kinggh0stee/WellD/hardware/pcb/interfaces.kicad_sch

## KiCad design hardware/pcb/interfaces.kicad_sch (2026-07-22, an earlier design)

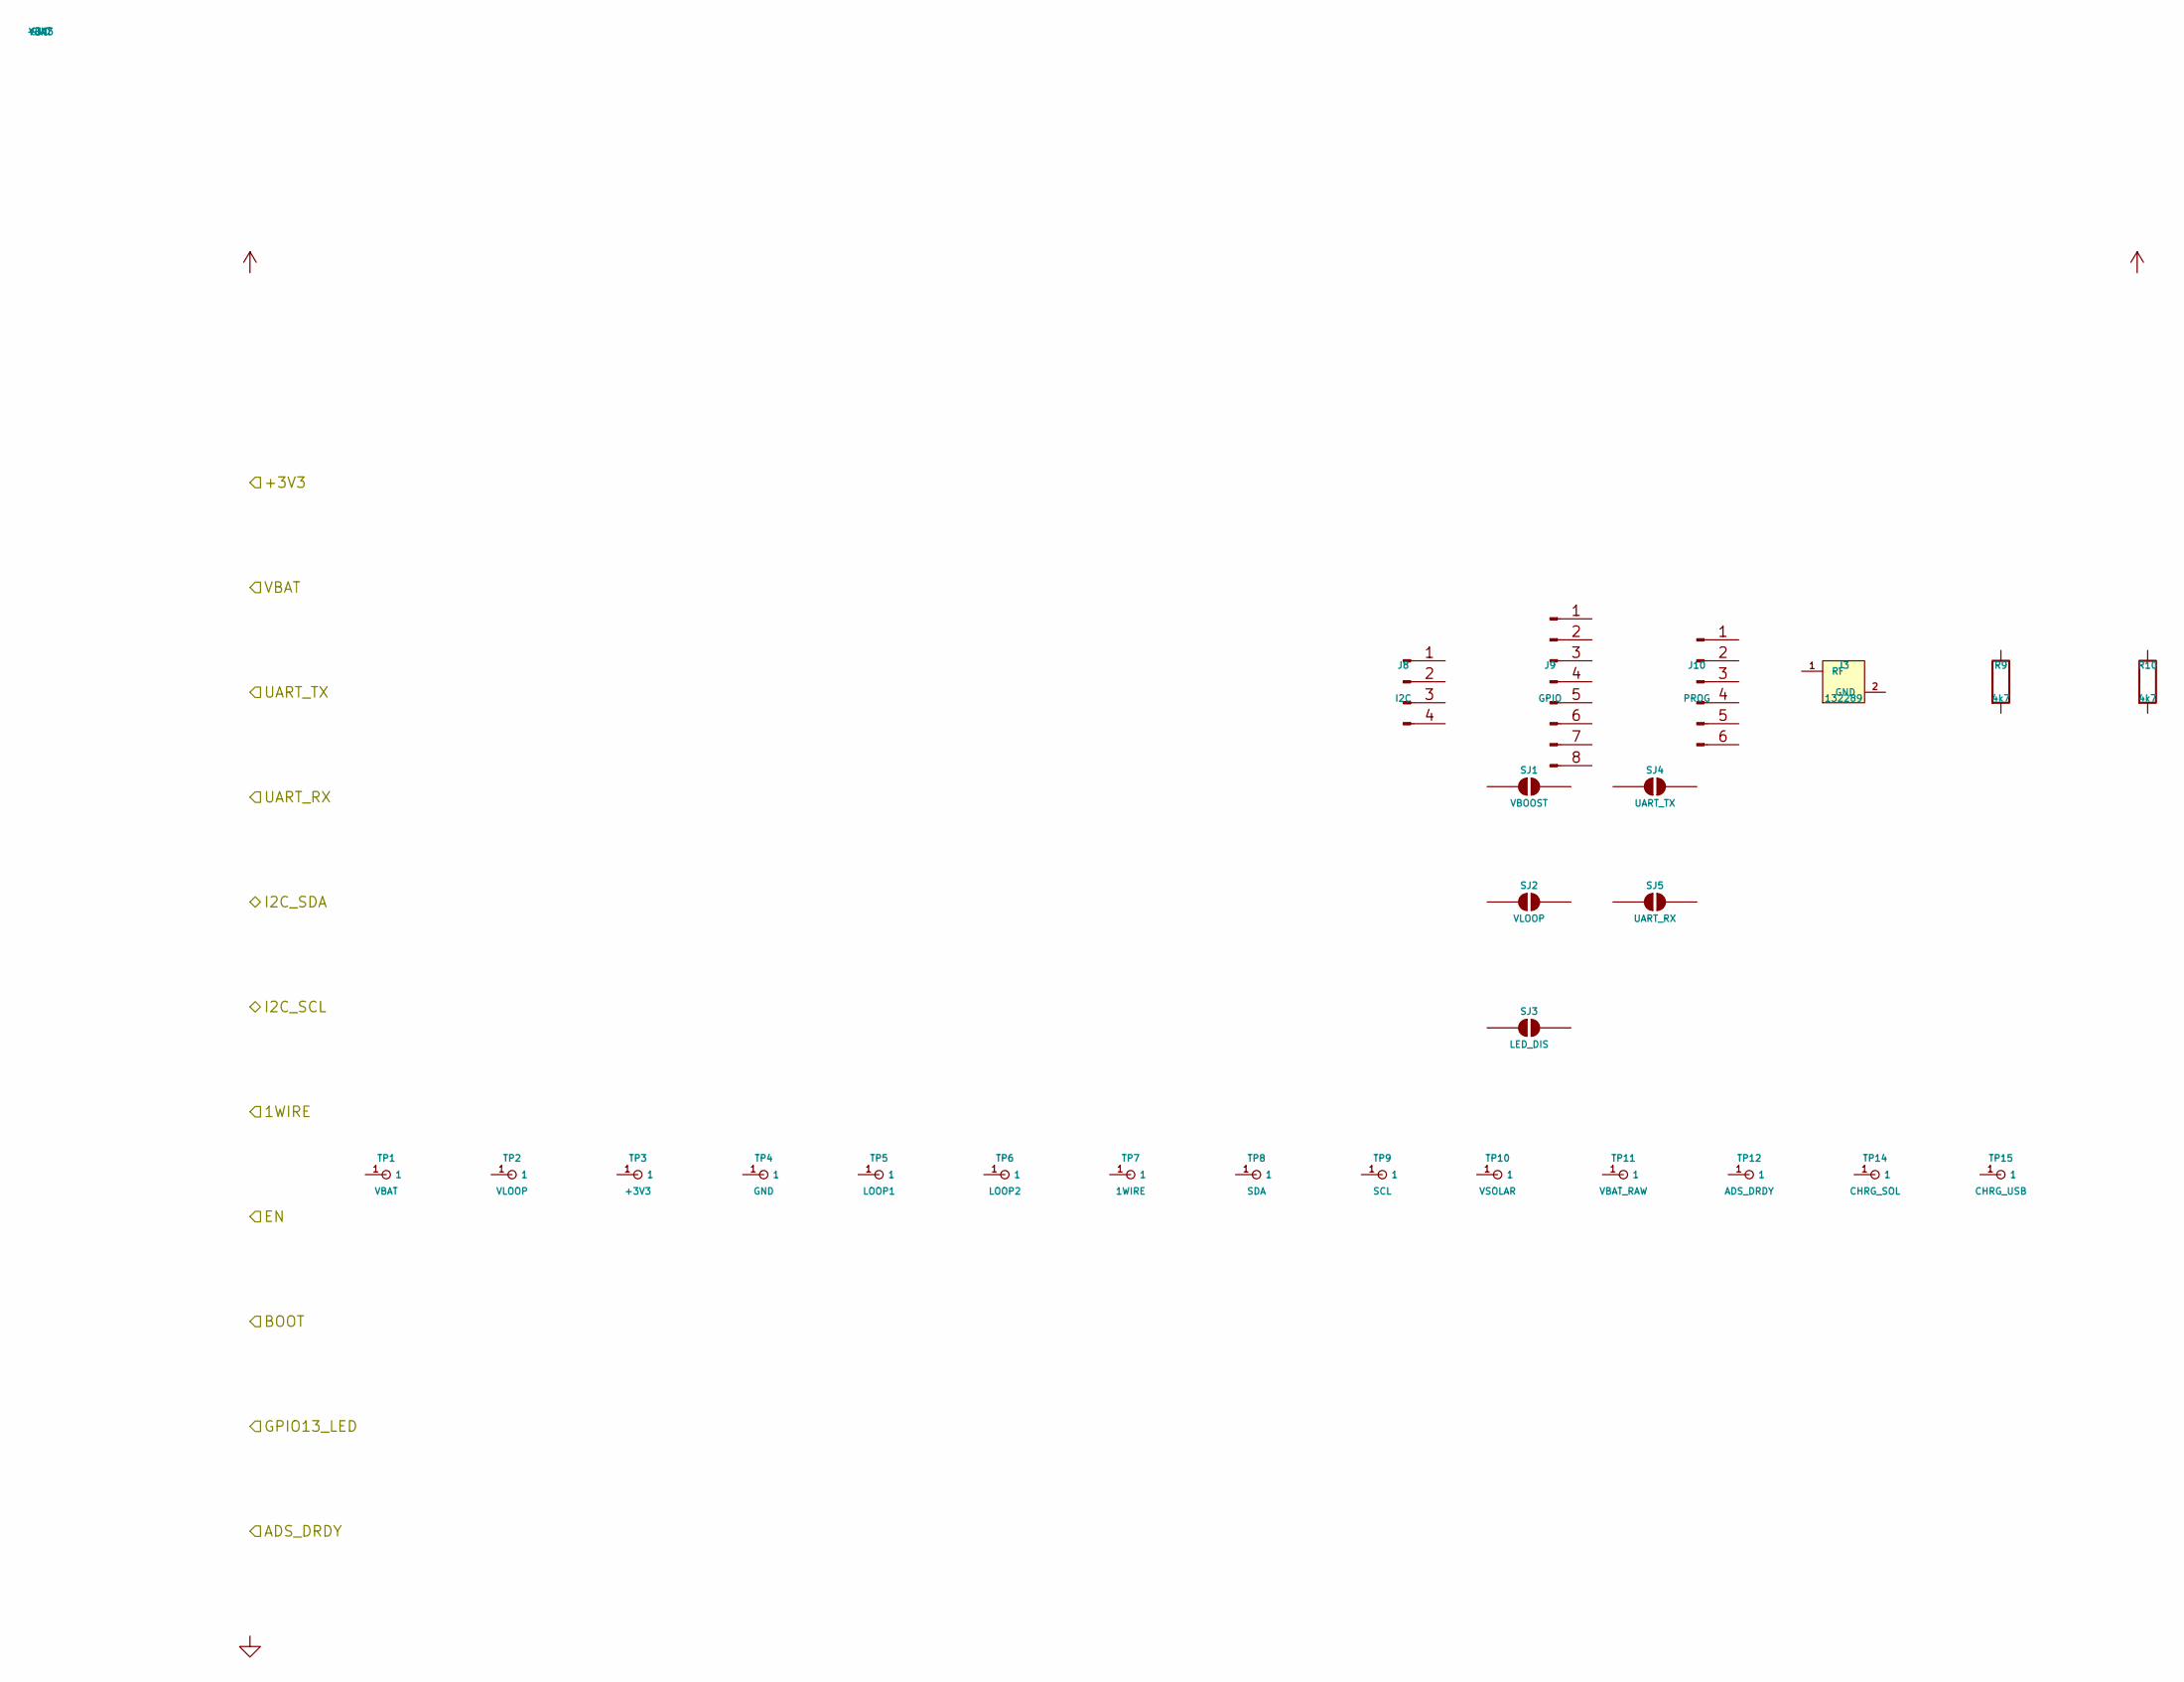
[picture p2: schematic interfaces.kicad_sch]

Parts:
J3: 132289; SMA_Amphenol_132289_EdgeMount
J8: I2C; PinHeader_1x04_P2.54mm_Vertical
J9: GPIO; PinHeader_1x08_P2.54mm_Vertical
J10: PROG; PinHeader_1x06_P1.27mm_Vertical
R9, R10: 4k7; R_0402_1005Metric
SJ1: VBOOST; SolderJumper-2_P1.3mm_Open_Pad1.0x1.5mm
SJ2: VLOOP; SolderJumper-2_P1.3mm_Open_Pad1.0x1.5mm
SJ3: LED_DIS; SolderJumper-2_P1.3mm_Open_Pad1.0x1.5mm
SJ4: UART_TX; SolderJumper-2_P1.3mm_Open_Pad1.0x1.5mm
SJ5: UART_RX; SolderJumper-2_P1.3mm_Open_Pad1.0x1.5mm
TP1: VBAT; TestPoint_Pad_1.0x1.0mm
TP2: VLOOP; TestPoint_Pad_1.0x1.0mm
TP3: +3V3; TestPoint_Pad_1.0x1.0mm
TP4: GND; TestPoint_Pad_1.0x1.0mm
TP5: LOOP1; TestPoint_Pad_1.0x1.0mm
TP6: LOOP2; TestPoint_Pad_1.0x1.0mm
TP7: 1WIRE; TestPoint_Pad_1.0x1.0mm
TP8: SDA; TestPoint_Pad_1.0x1.0mm
TP9: SCL; TestPoint_Pad_1.0x1.0mm
TP10: VSOLAR; TestPoint_Pad_1.0x1.0mm
TP11: VBAT_RAW; TestPoint_Pad_1.0x1.0mm
TP12: ADS_DRDY; TestPoint_Pad_1.0x1.0mm
TP14: CHRG_SOL; TestPoint_Pad_1.0x1.0mm
TP15: CHRG_USB; TestPoint_Pad_1.0x1.0mm
