kinggh0stee/WellD/hardware/pcb/power.kicad_sch

## KiCad design hardware/pcb/power.kicad_sch (2026-07-22, an earlier design)

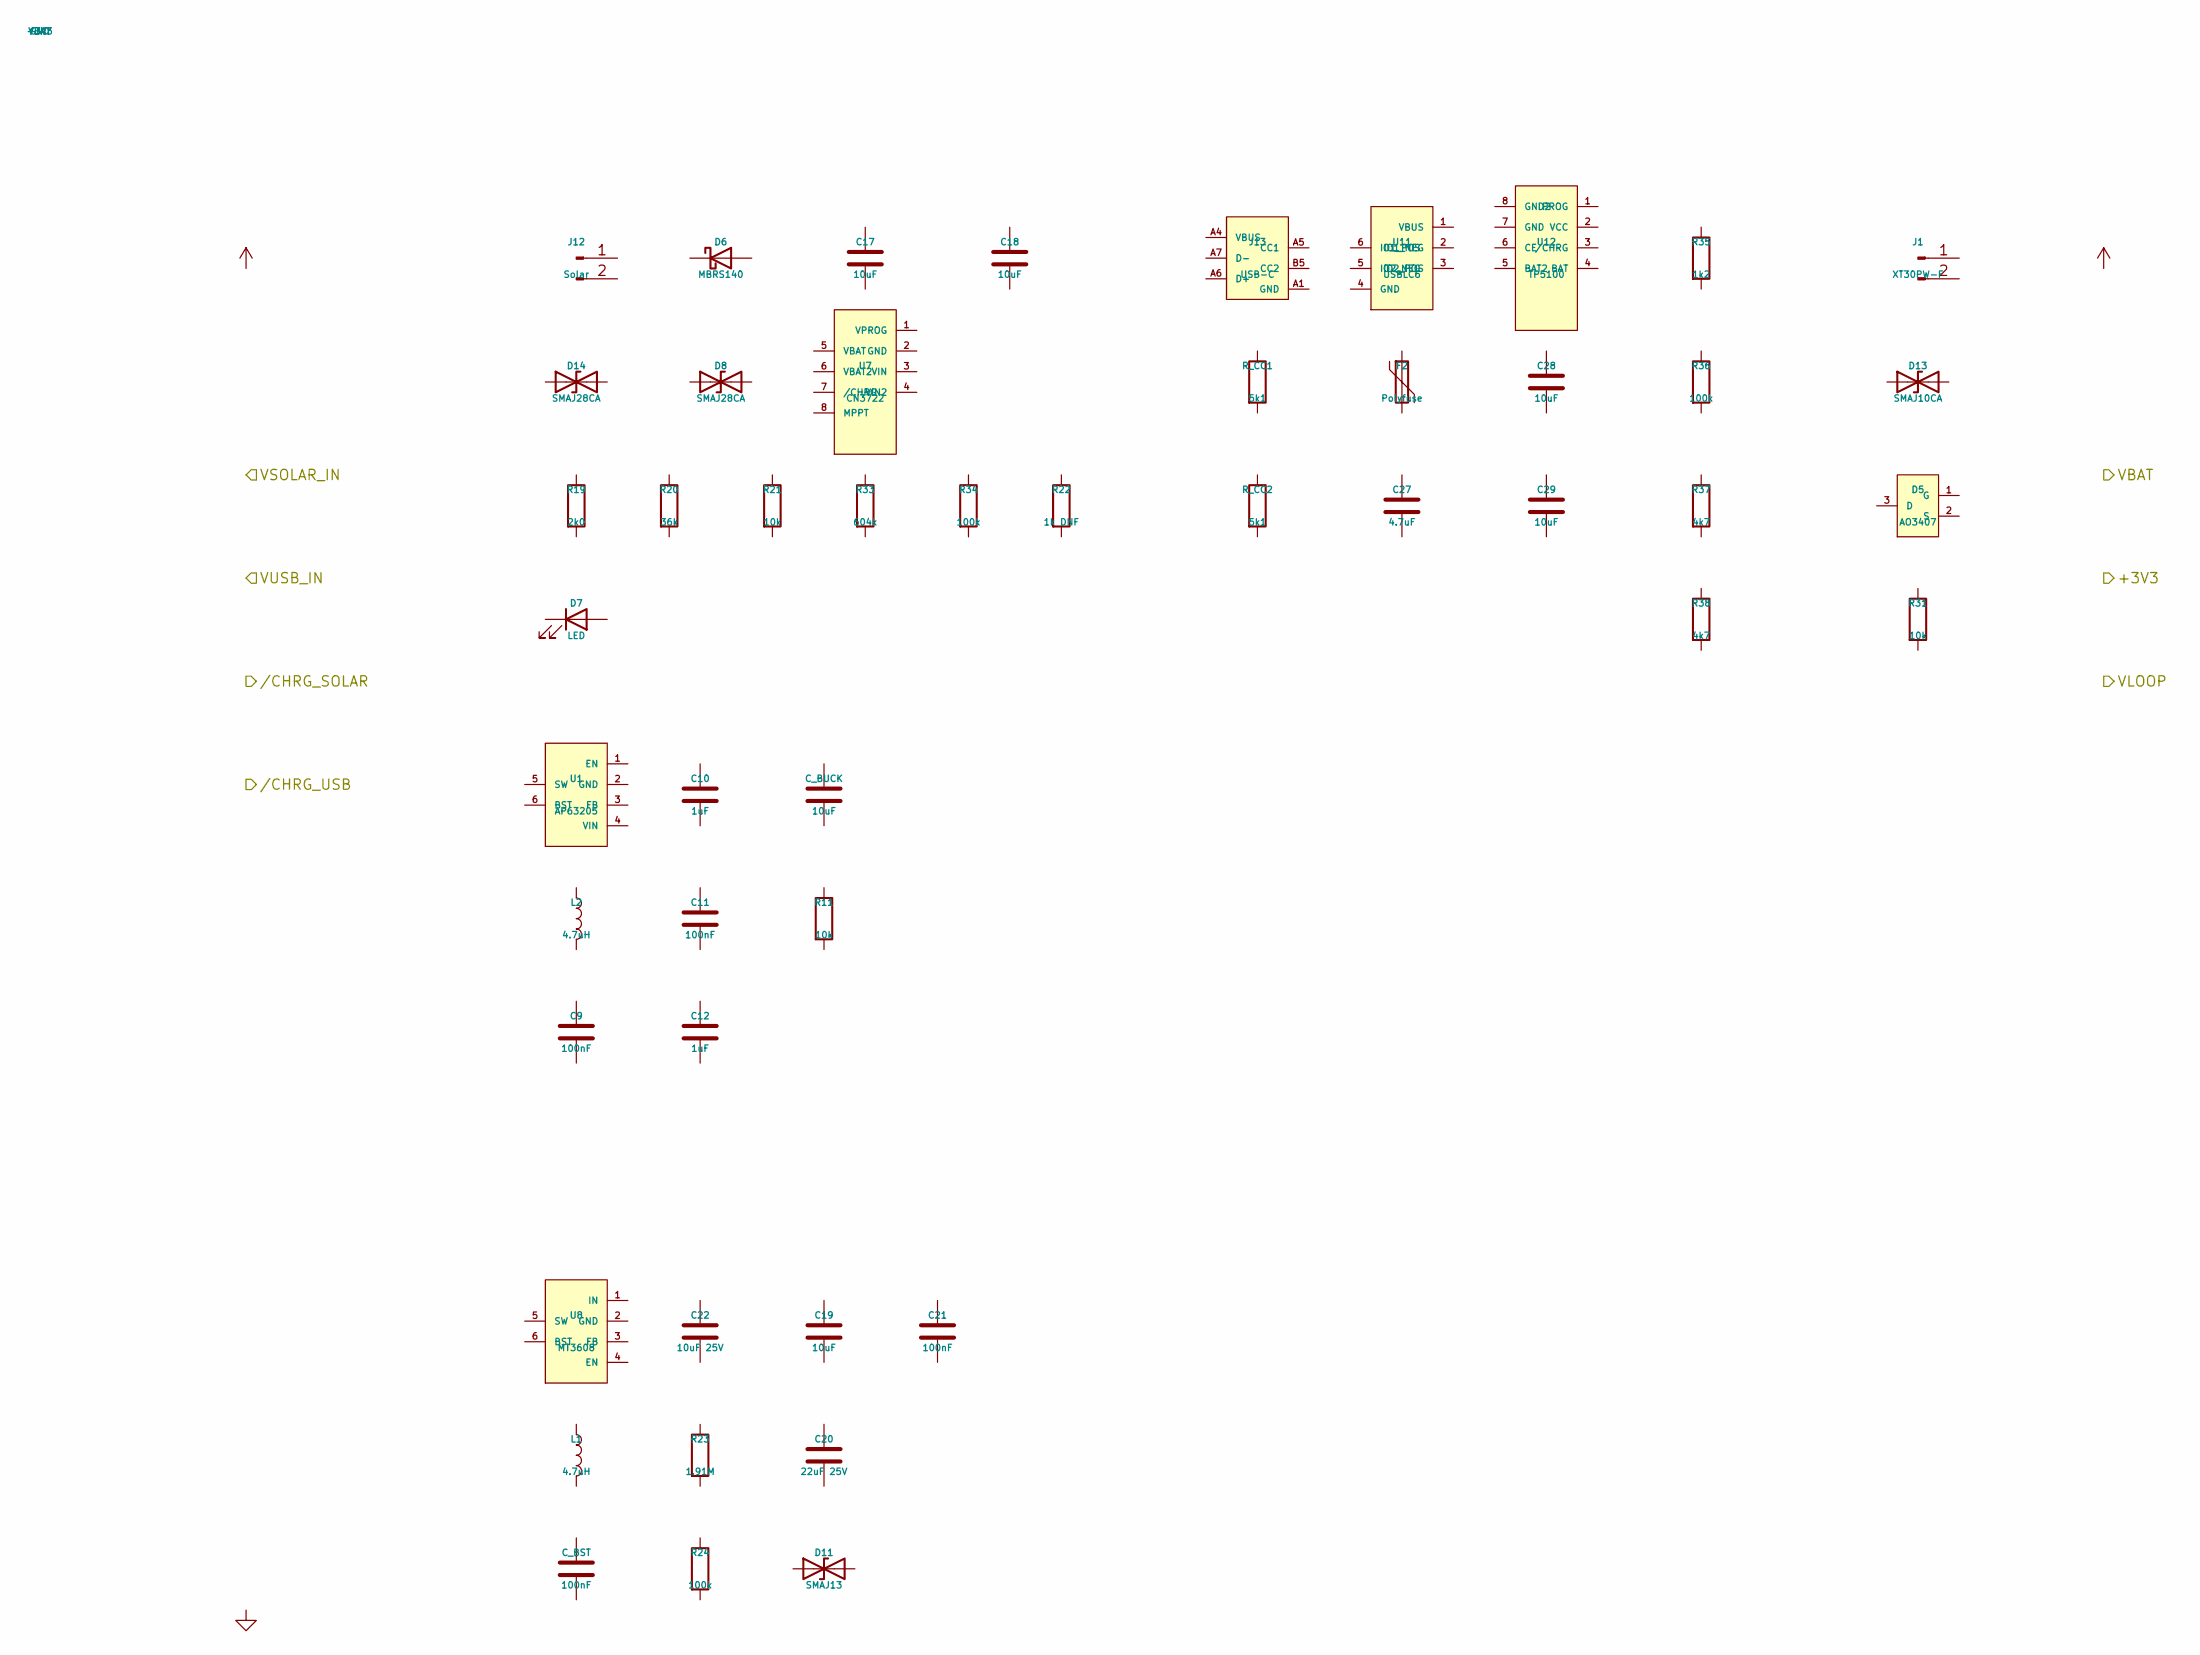
[picture p5: schematic power.kicad_sch]

Parts:
C9, C11, C21: 100nF; C_0402_1005Metric
C10, C12: 1uF; C_0402_1005Metric
C17, C18, C19, C28, C29: 10uF; C_0805_2012Metric
C20: 22uF 25V; C_1206_3216Metric
C22: 10uF 25V; C_0805_2012Metric
C27: 4.7uF; C_0805_2012Metric
C_BST: 100nF; C_0402_1005Metric; LCSC C14663
C_BUCK: 10uF; C_0805_2012Metric
D5: AO3407; SOT-23; LCSC C31417
D6: MBRS140; D_SOD-123
D7: LED; LED_0603_1608Metric
D8, D14: SMAJ28CA; D_SMA
D11: SMAJ13; D_SMA; LCSC C8057
D13: SMAJ10CA; D_SMA; LCSC C2836474
F2: Polyfuse; Fuse_1206_3216Metric
J1: XT30PW-F; XT30PW-F_RightAngle; LCSC C601498
J12: Solar; TerminalBlock_Phoenix_PT-1,5-2-3.5-H_1x02_P3.50mm_Horizontal
J13: USB-C; USB_C_Receptacle_GCT_USB4135-GF-A_6P_TopMnt_Horizontal
L1, L2: 4.7uH; L_Vishay_IFSC-1515AH_4x4x1.8mm; LCSC C376098
R11, R21, R31: 10k; R_0402_1005Metric
R19: 2k0; R_0402_1005Metric
R20: 36k; R_0402_1005Metric
R22: 1k DNF; R_0402_1005Metric
R23: 1.91M; R_0402_1005Metric
R24, R34, R36: 100k; R_0402_1005Metric
R33: 604k; R_0402_1005Metric
R35: 1k2; R_0402_1005Metric
R37, R38: 4k7; R_0402_1005Metric
R_CC1, R_CC2: 5k1; R_0402_1005Metric
U1: AP63205; SOT-23-6; LCSC C2862534
U7: CN3722; SOIC-8_3.9x4.9mm_P1.27mm; LCSC C2690716
U8: MT3608; SOT-23-6; LCSC C84005
U11: USBLC6; SOT-23-6; LCSC C7519
U12: TP5100; SOIC-8_3.9x4.9mm_P1.27mm; LCSC C841540
