kinggh0stee/WellD/hardware/pcb/sensors.kicad_sch

## KiCad design hardware/pcb/sensors.kicad_sch (2026-07-22, an earlier design)

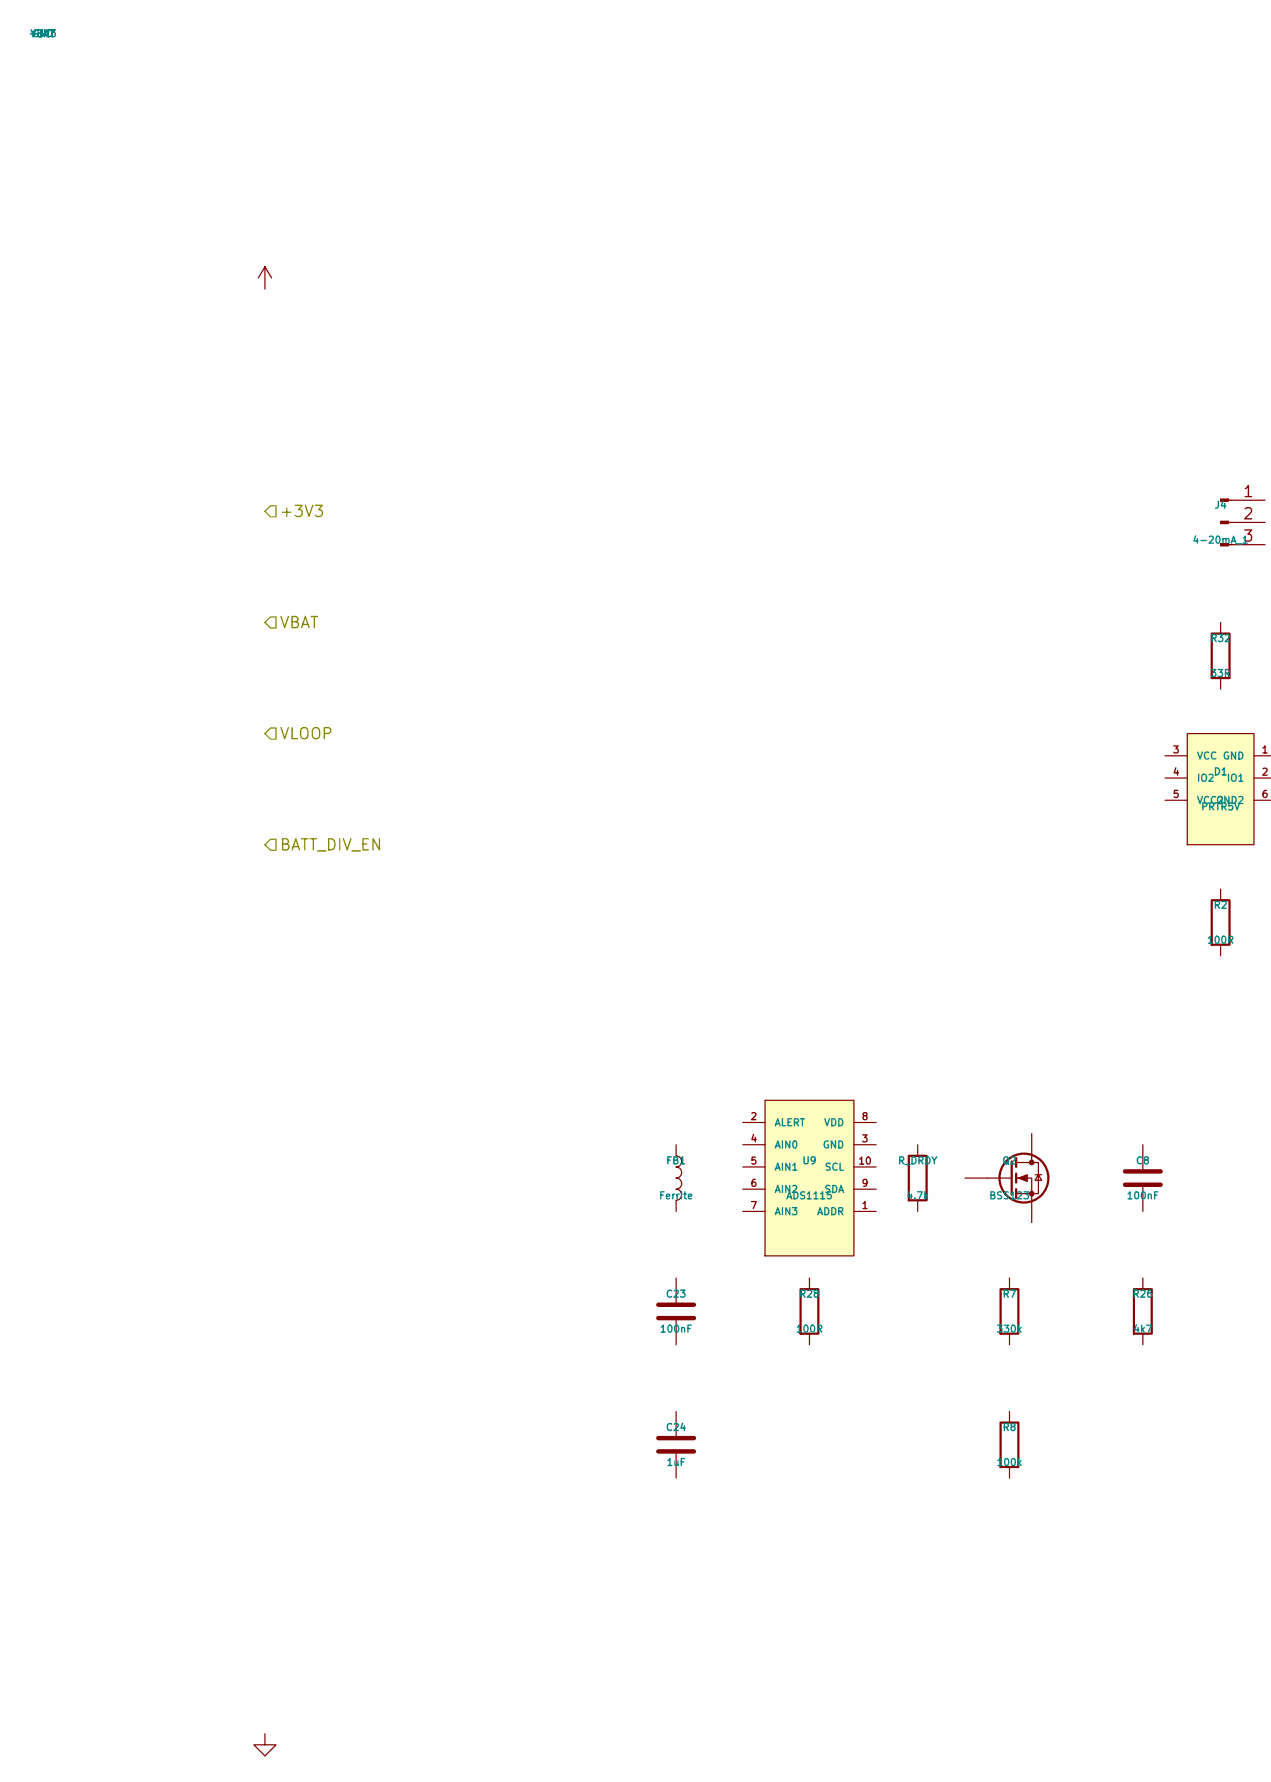
[picture p6: schematic sensors.kicad_sch, part in row 1, column 1]

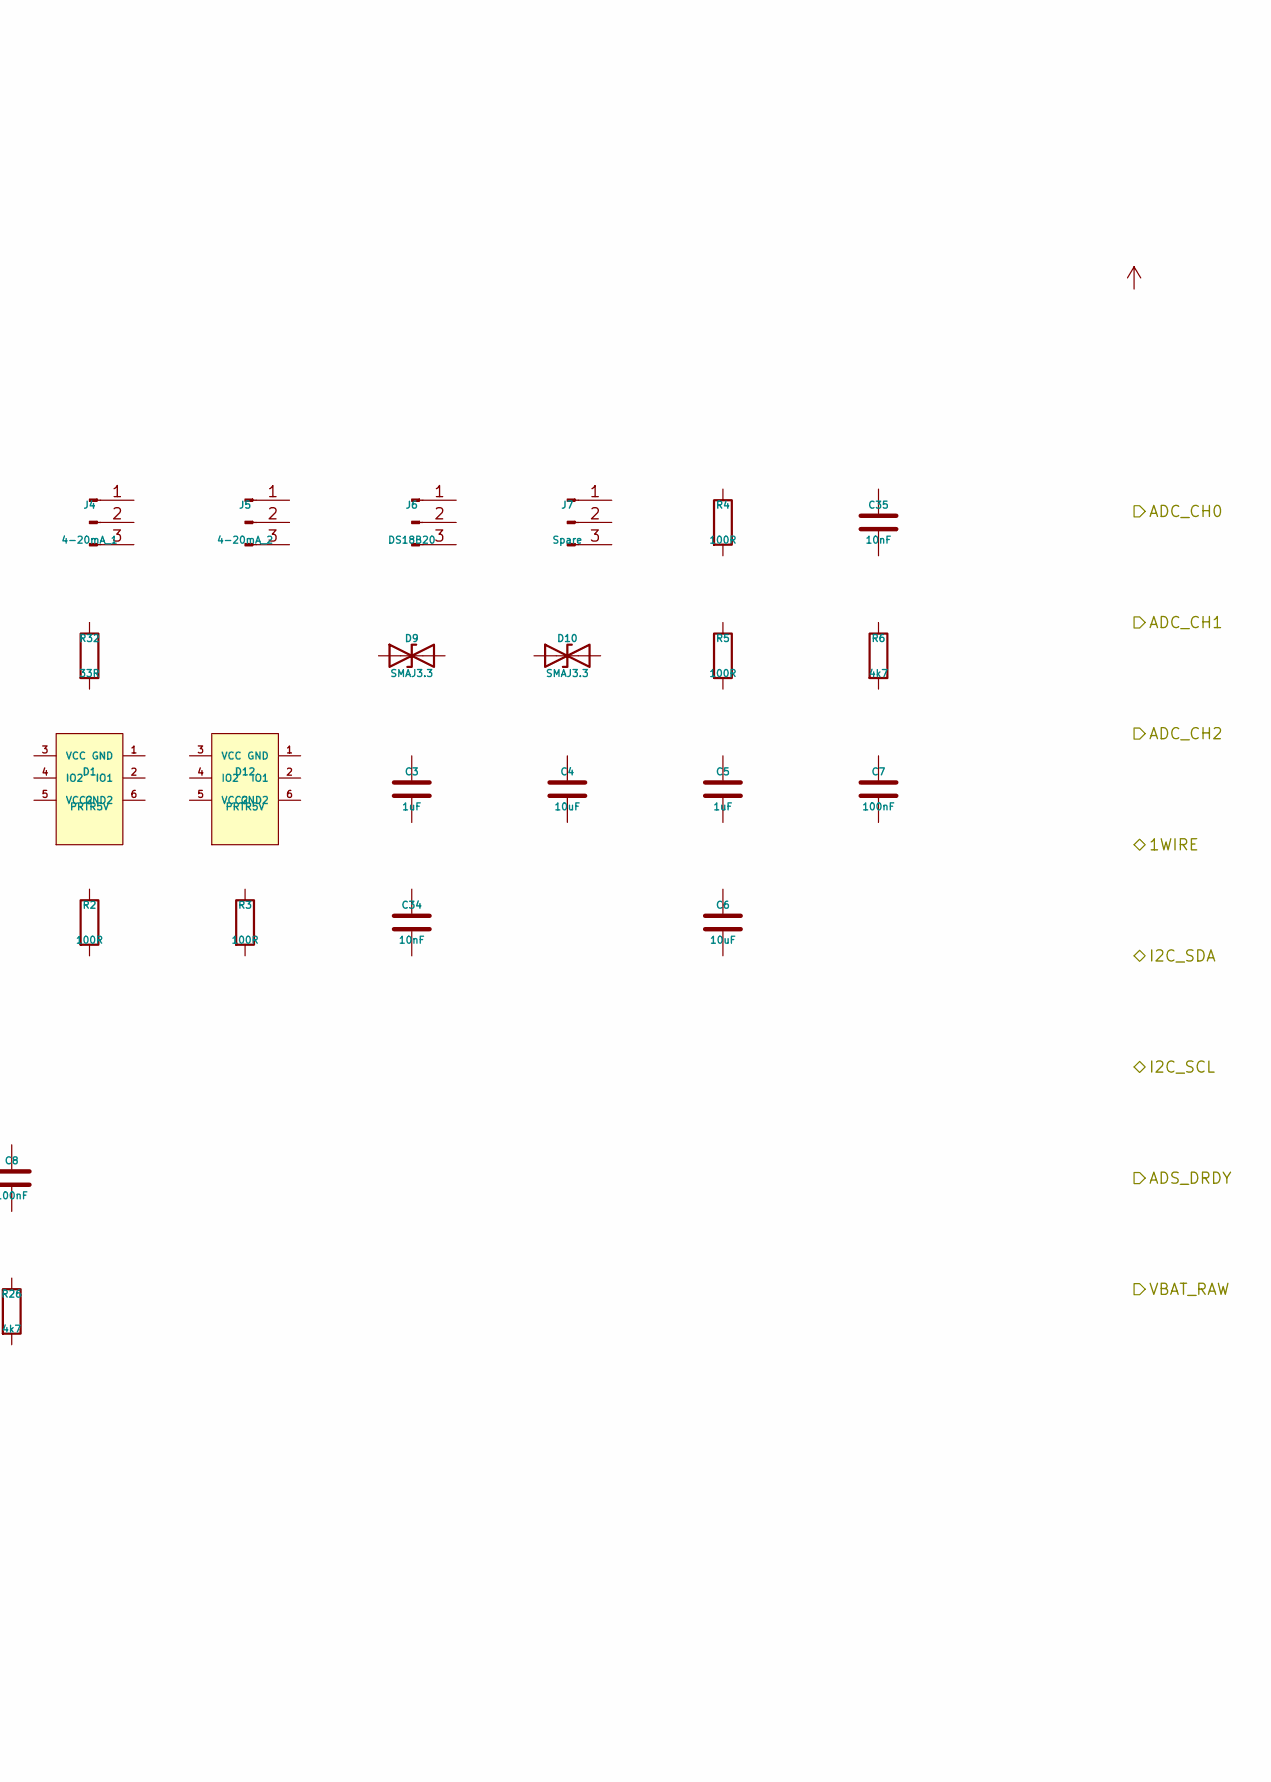
[picture p7: schematic sensors.kicad_sch, part in row 1, column 2]

Parts:
C3, C5, C24: 1uF; C_0402_1005Metric
C4, C6: 10uF; C_0805_2012Metric
C7, C8, C23: 100nF; C_0402_1005Metric
C34, C35: 10nF; C_0402_1005Metric
D1, D12: PRTR5V; SOT-363_SC-70-6; LCSC C2687116
D9, D10: SMAJ3.3; D_SMA; LCSC C2836497
FB1: Ferrite; L_0402_1005Metric; LCSC C76537
J4: 4-20mA_1; TerminalBlock_Phoenix_PT-1,5-3-3.5-H_1x03_P3.50mm_Horizontal
J5: 4-20mA_2; TerminalBlock_Phoenix_PT-1,5-3-3.5-H_1x03_P3.50mm_Horizontal
J6: DS18B20; TerminalBlock_Phoenix_PT-1,5-3-3.5-H_1x03_P3.50mm_Horizontal
J7: Spare; TerminalBlock_Phoenix_PT-1,5-3-3.5-H_1x03_P3.50mm_Horizontal
Q2: BSS123; SOT-23
R2, R4: 100R; R_0805_2012Metric
R3, R5, R28: 100R; R_0402_1005Metric
R6, R26: 4k7; R_0402_1005Metric
R7: 330k; R_0402_1005Metric
R8: 100k; R_0402_1005Metric
R32: 33R; R_0402_1005Metric
R_DRDY: 4.7k; R_0402_1005Metric
U9: ADS1115; MSOP-10_3x3mm_P0.5mm; LCSC C37593
