kinggh0stee/WellD/hardware/pcb_old/mcu.kicad_sch

## KiCad design hardware/pcb_old/mcu.kicad_sch (2026-05-25, an earlier design)


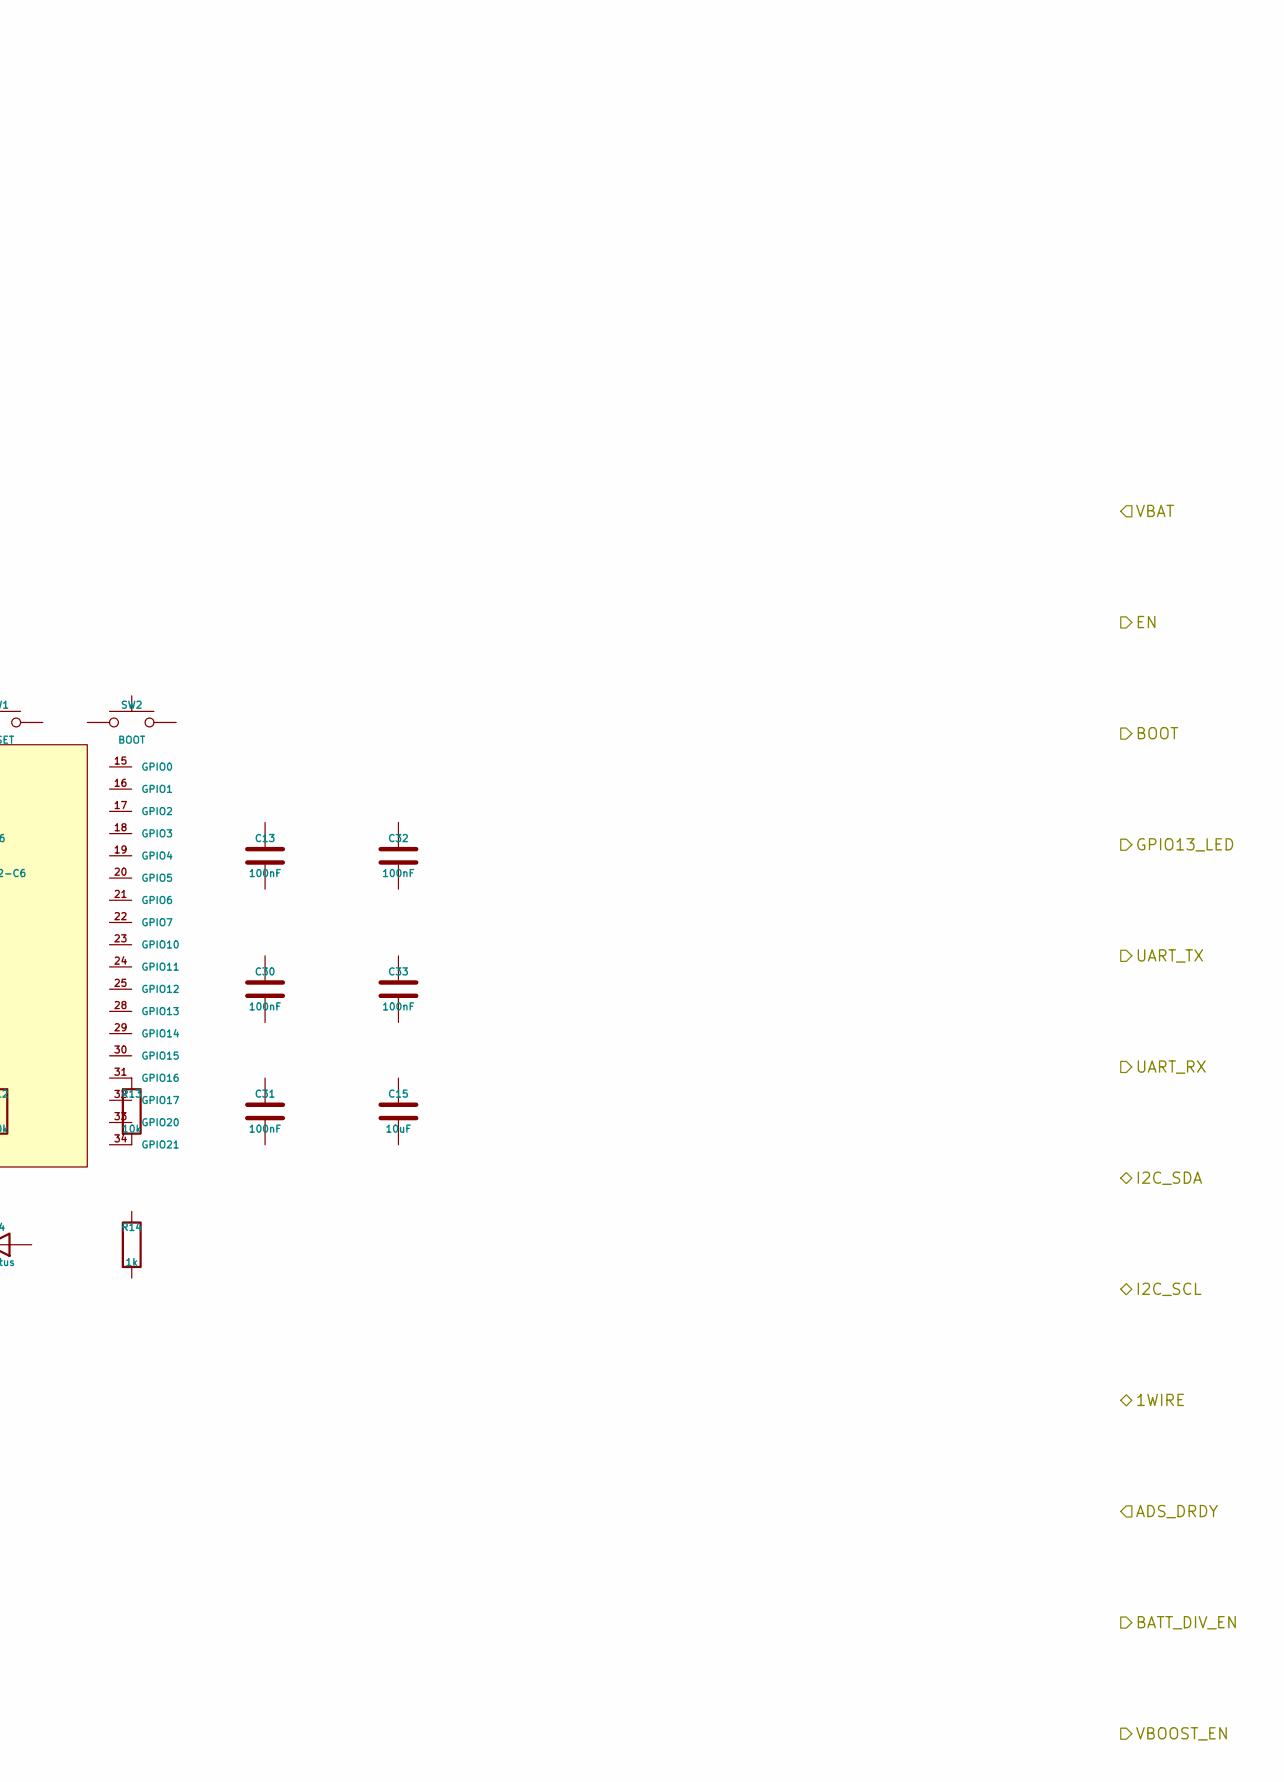
[picture p8: schematic mcu.kicad_sch, part in row 1, column 2]

Parts:
C13, C30, C31, C32, C33: 100nF; C_0402_1005Metric
C15: 10uF; C_0805_2012Metric
D4: Status; LED_0603_1608Metric
R12, R13: 10k; R_0402_1005Metric
R14: 1k; R_0402_1005Metric
SW1: RESET; SW_Push_1P1T_NO_CK_KSC6xxG
SW2: BOOT; SW_Push_1P1T_NO_CK_KSC6xxG
U6: ESP32-C6; ESP32-C6-MINI-1U
